Acolhuuua/LowProfileAcrylicArcadeStick/CADFiles/STL/SpringBaseBottomSlimVersionLight.stl

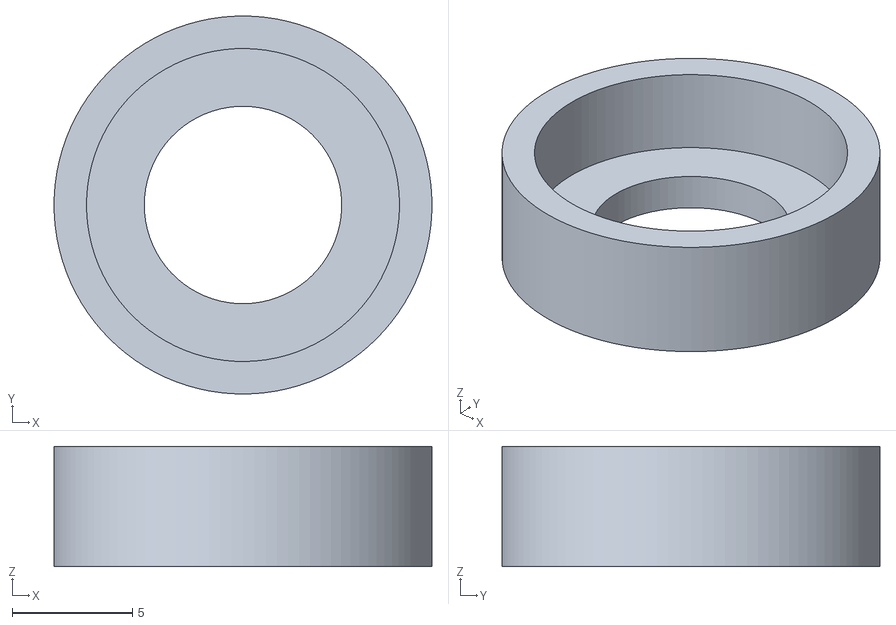
[picture p15: CAD file, 2026-05-24]
CADFiles/STL/SpringBaseBottomSlimVersionLight.stl
15.7 x 15.7 x 5.00
