Acolhuuua/LowProfileAcrylicArcadeStick/CADFiles/STL/PCBContainerTOPHoneyComb.stl

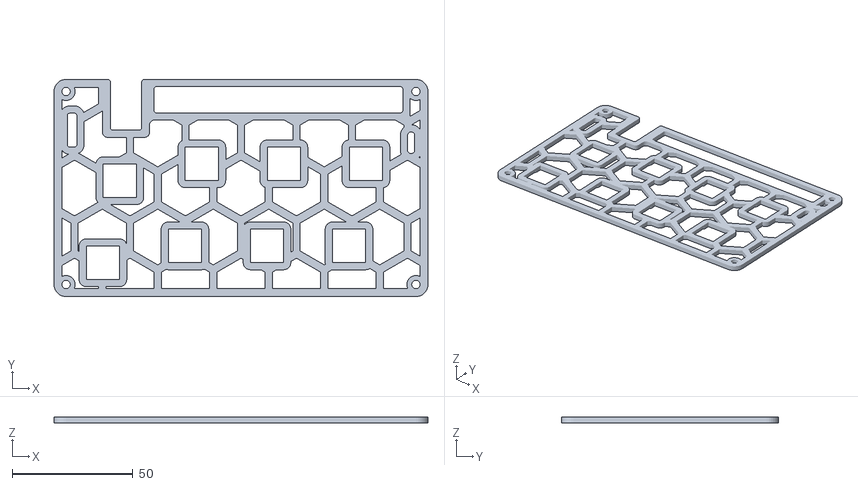
[picture p16: CAD file, 2026-05-24]
CADFiles/STL/PCBContainerTOPHoneyComb.stl
155.0 x 90.0 x 2.50
